holla2040/WarmDirt/board/WarmDirt-pcb.png

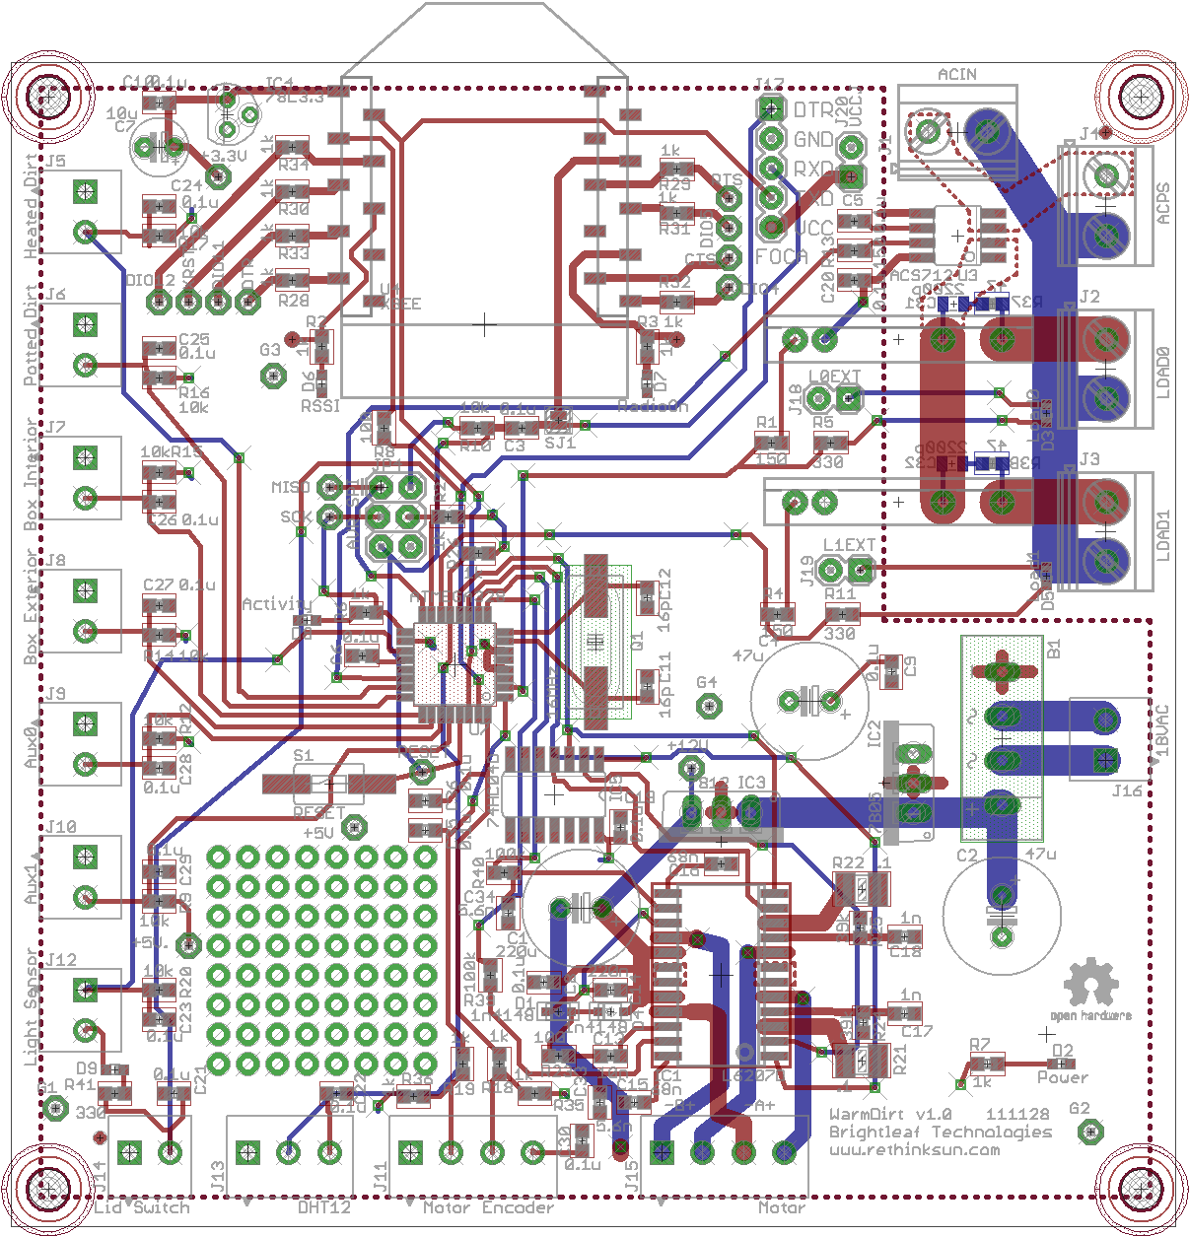
board/WarmDirt-pcb.png
