holla2040/WarmDirt/board/WarmDirt-sch.png

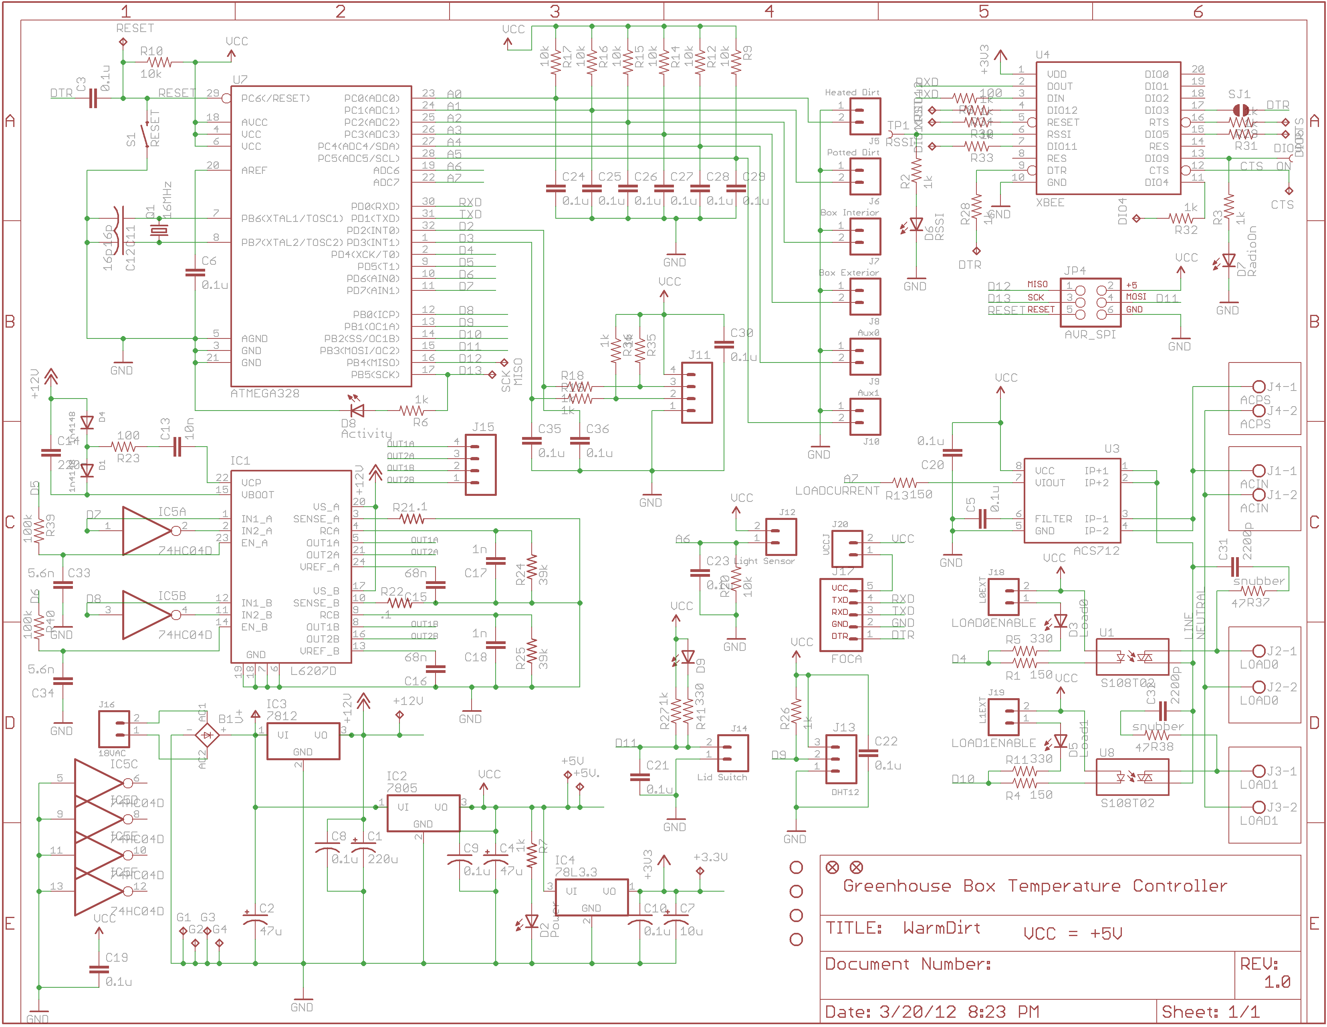
board/WarmDirt-sch.png
