holla2040/WarmDirt/docs/seeed - 10k3950.jpg

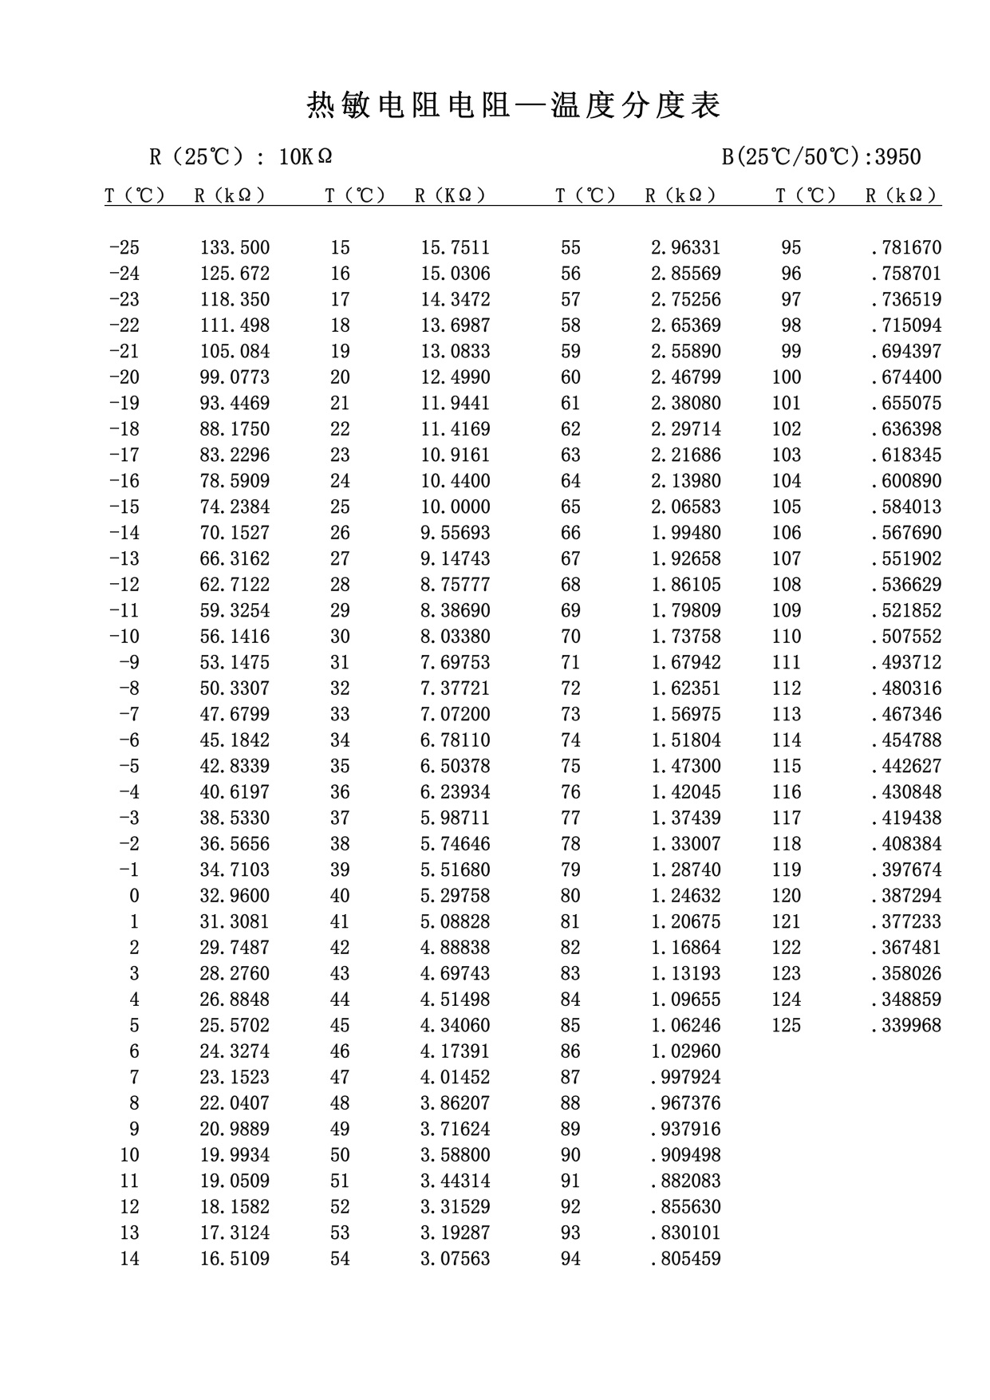
docs/seeed - 10k3950.jpg
