holla2040/WarmDirt/images/111230-093112.jpg

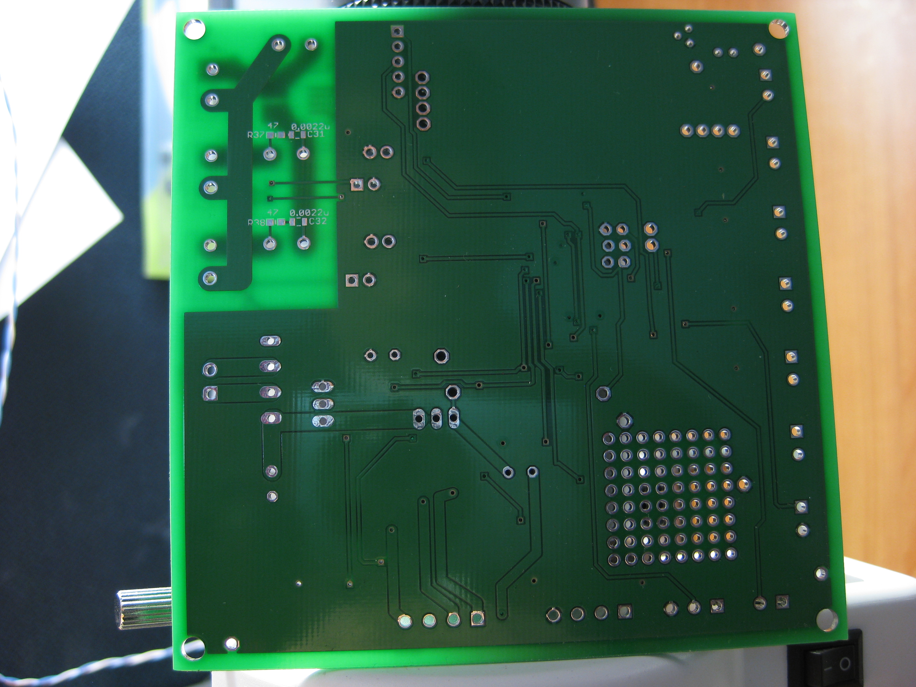
images/111230-093112.jpg
