holla2040/WarmDirt/images/111230-093212.jpg

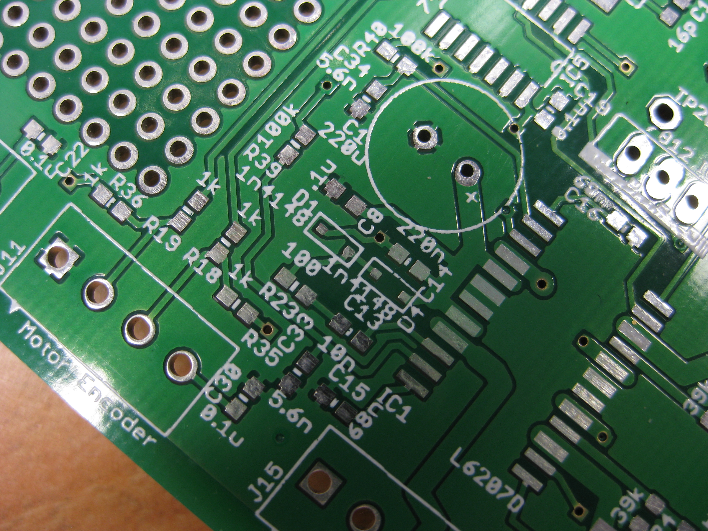
images/111230-093212.jpg
