holla2040/WarmDirt/images/111230-093306.jpg

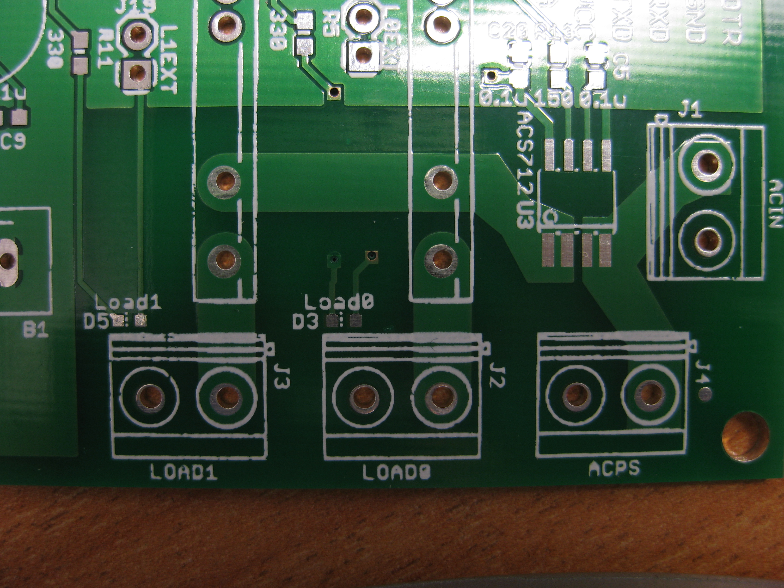
images/111230-093306.jpg
