holla2040/WarmDirt/images/111230-093437.jpg

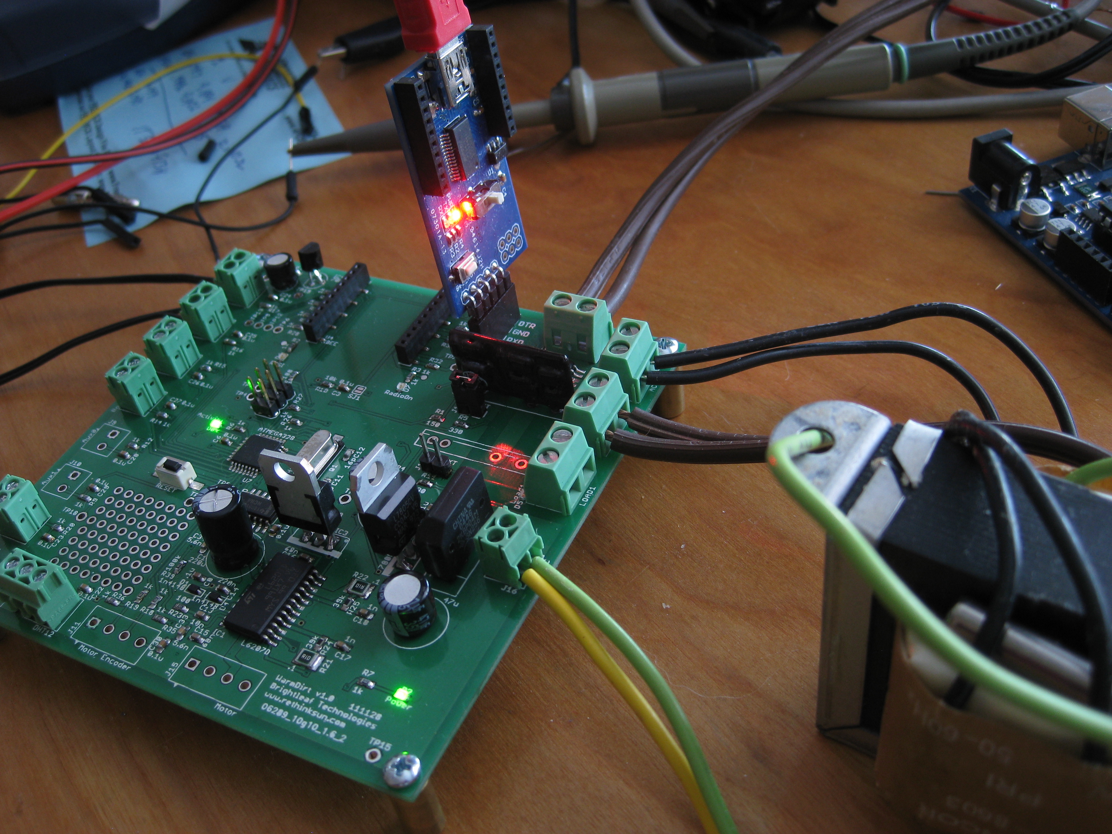
images/111230-093437.jpg
