holla2040/WarmDirt/images/111230-174920.jpg

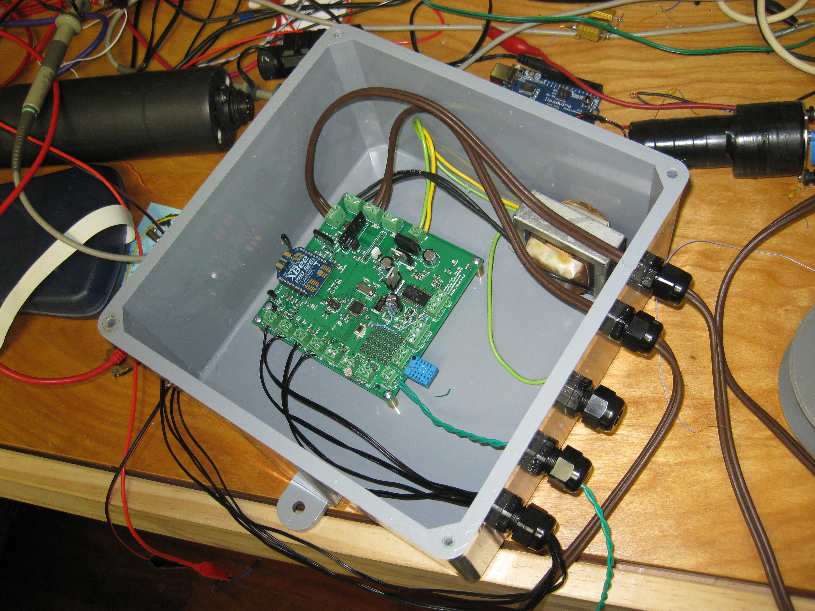
images/111230-174920.jpg
