holla2040/WarmDirt/images/120122-201555.jpg

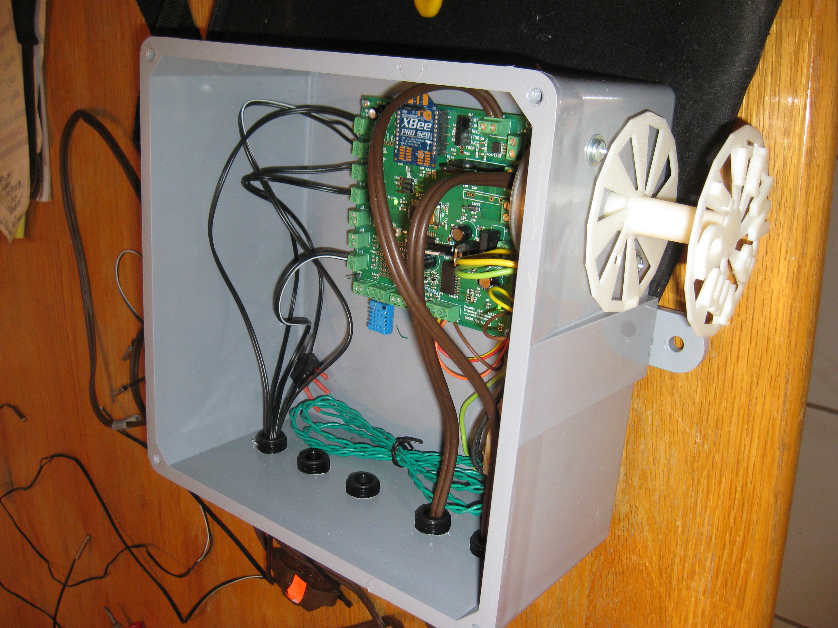
images/120122-201555.jpg
