holla2040/WarmDirt/images/120122-201719.jpg

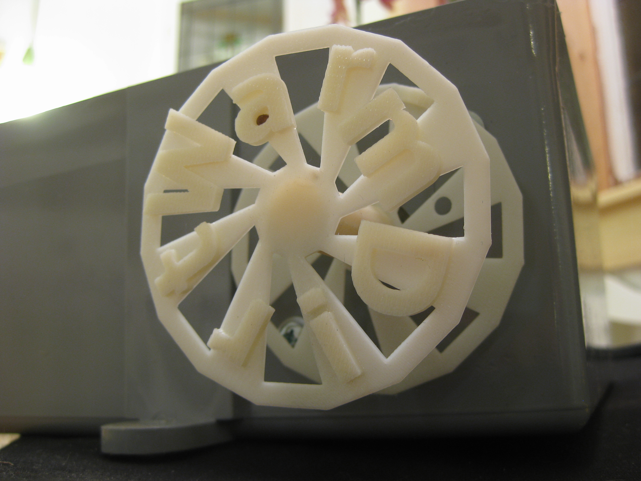
images/120122-201719.jpg
