holla2040/WarmDirt/images/120122-201806.jpg

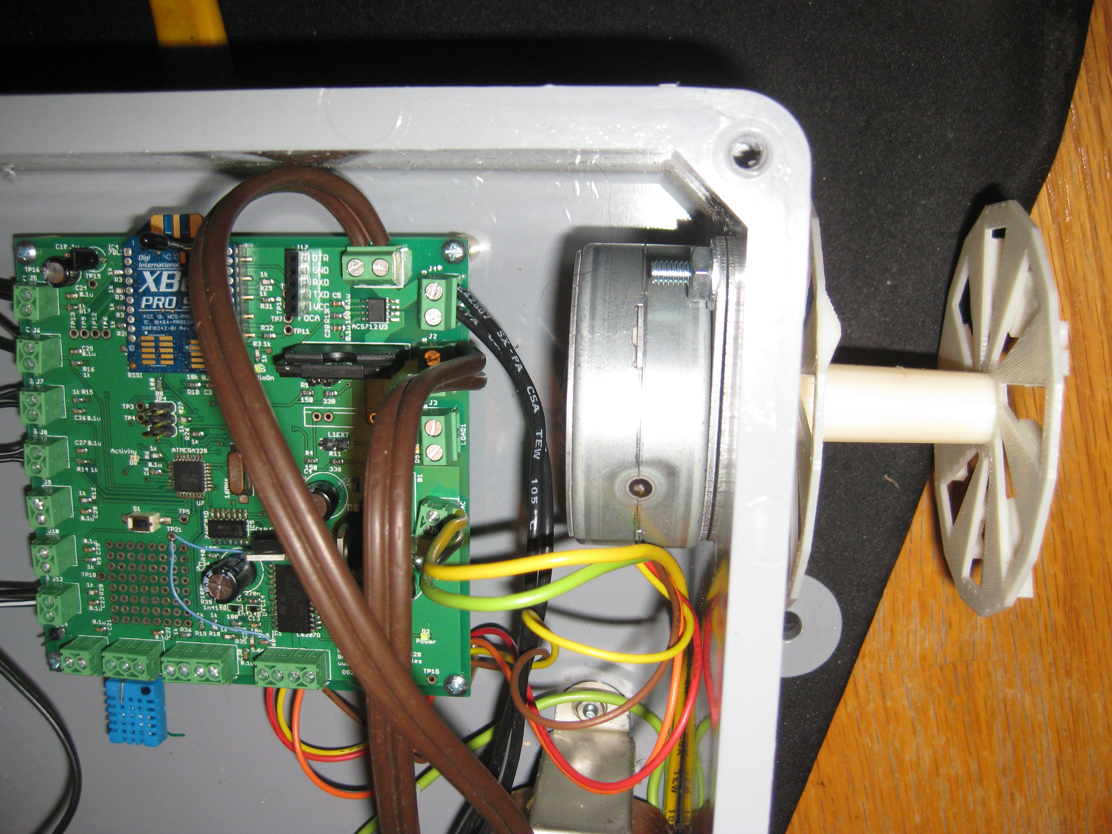
images/120122-201806.jpg
