holla2040/WarmDirt/images/120303-230120.jpg

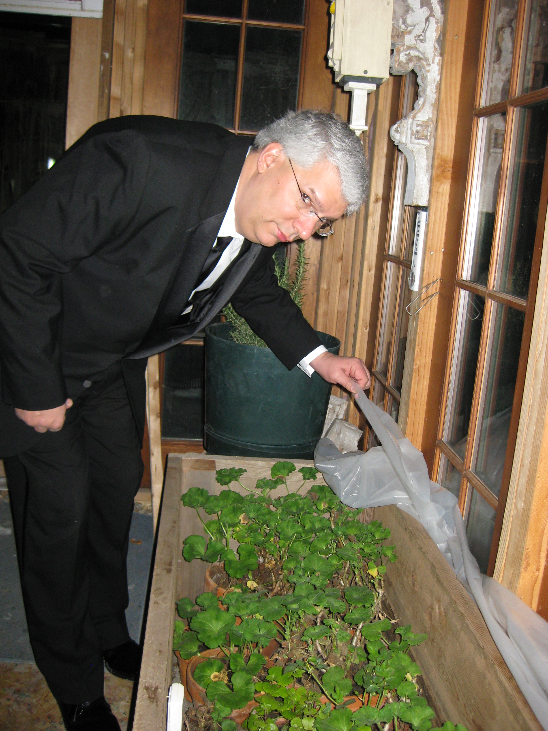
images/120303-230120.jpg
