holla2040/WarmDirt/images/120317-151152.jpg

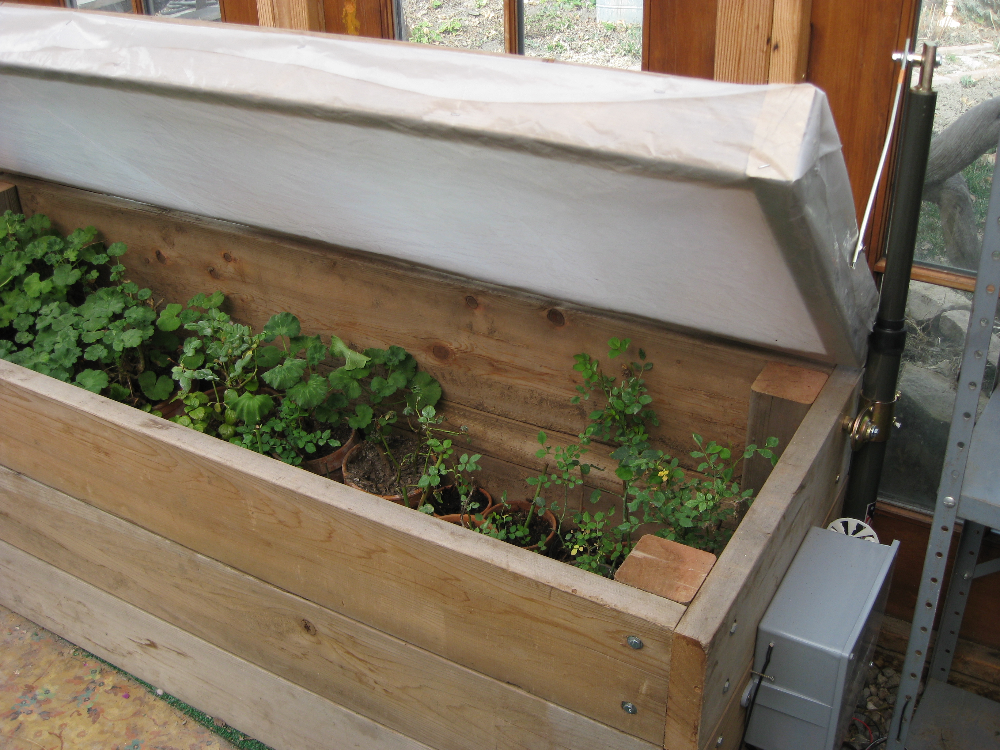
images/120317-151152.jpg
