holla2040/WarmDirt/images/120317-151209.jpg

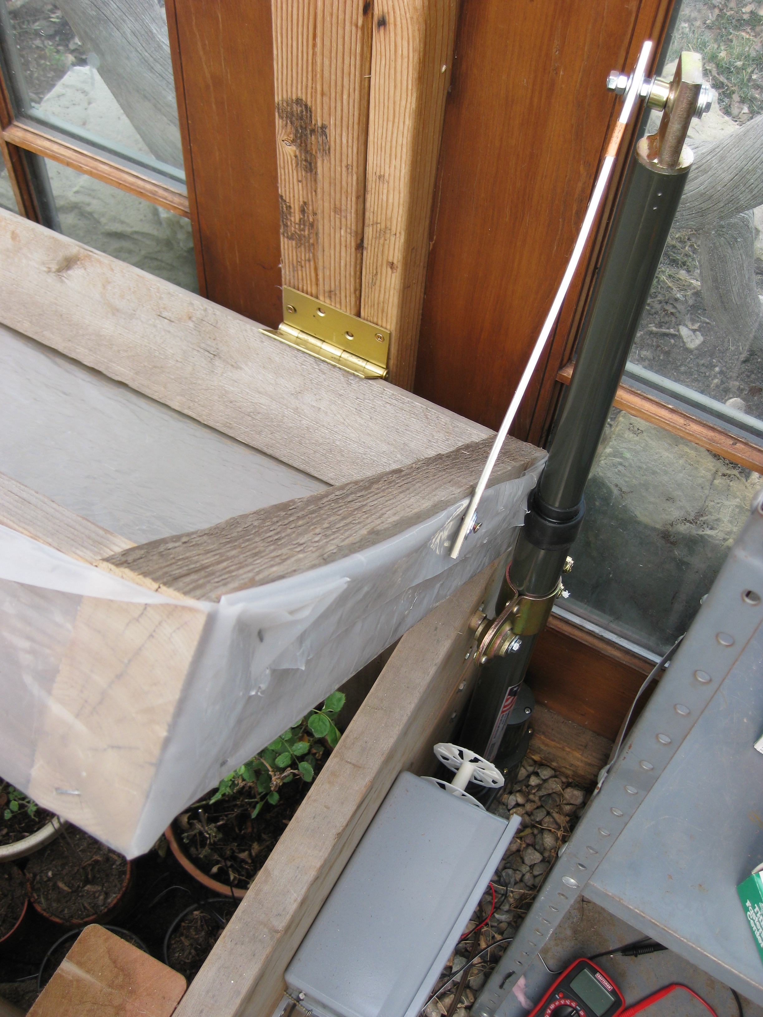
images/120317-151209.jpg
